frohro/Intro-to-CAD-2026/v0.1/README.md

# Board v0.1

## Hardware

Open [`Hardware/Intro-to-CAD-2026.kicad_pro`](Hardware/Intro-to-CAD-2026.kicad_pro).

## Software

| Path | Role |
|---|---|
| `Software/SDR/MicroPythonSDR/` | Pico MicroPython + Quisk helpers |
| `Software/SDR/Soapy-For-2026-Board/` | Soapy module (from master) |
| `Software/SDR/firmware/96_kHz_2026/` | C UAC1 firmware (restore if missing) |

See `Software/SDR/firmware/README.md` if the firmware folder is empty.
