frohro/Intro-to-CAD-2026/v0.1/Software/SDR/README.md

# v0.1 Software / SDR

- **MicroPythonSDR/** — board Python, Quisk configs/widgets
- **Soapy-For-2026-Board/** — SoapySDR support module
- **firmware/** — native Pico UAC1 projects (see firmware/README.md)
