frohro/Intro-to-CAD-2026/v0.1/Software/SDR/firmware/README.md

# v0.1 SDR firmware

| Folder | Description |
|---|---|
| `96_kHz_2026/` | PCM1808 96 kHz UAC1 firmware for the v0.1 board |

Source: `cptr-480-2026-instructor/Research/96_kHz_2026` (see `README_96kHz_v0.1.md` inside).
