frohro/Intro-to-CAD-2026/v0.2/Hardware/C18594.step

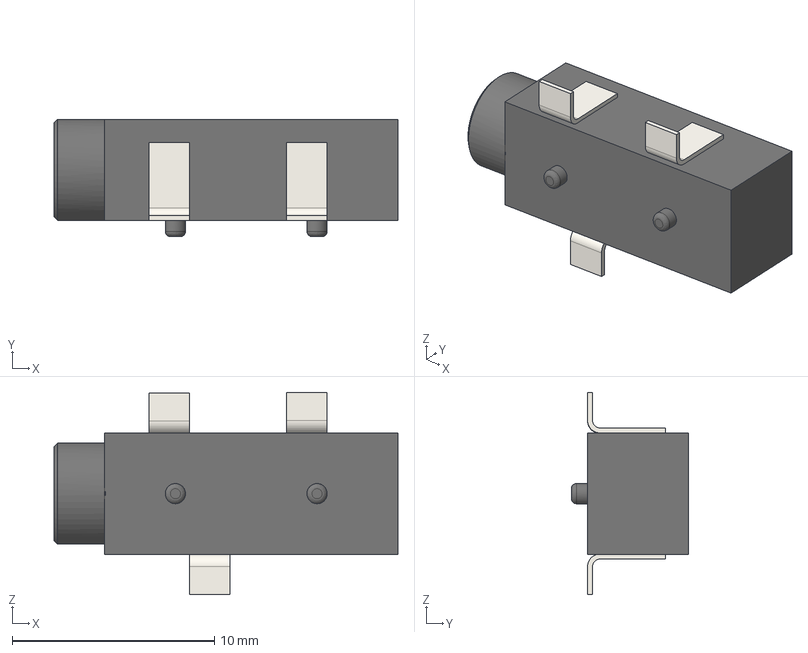
[picture p18: CAD file, 2026-07-31]
v0.2/Hardware/C18594.step
17.0 x 5.80 x 9.98 mm
sj-3524-smt-tr-pi v1 x 5
sj-3524-smt-tr-pi v002 x 5
sj-3524-smt-tr-pi v003 x 2
sj-3524-smt-tr-pi v004 x 2
