frohro/Intro-to-CAD-2026/v0.2/Hardware/Frohne/Docs/DAC_Amp_VBE_Mult.asc

C1: cap; 10µ
C2: cap; 100µ
Q1: npn; FMMT491
Q2: pnp; FMMT591
Q3: npn; FMMT491
R1: res; 1k
R2: res; 10k
R3: res; 2
R4: res; 2
R5: res; 5.1k
R6: res; 5.1k
R7: res; 2.2k
R8: res; 2.2k
R9: res; 32
R10: res; 1k
R11: res; 1k
U1: opamp2; OPA161x
V1: voltage; 5
V2: voltage; SINE(1.6 0.05 10000); Rser=100
Named nets: 0, VCC, VH, Vo, Vi
.tran 0 0.11 0.109
.lib OPA161x.LIB
.include FMMT491.spice.txt
.include FMMT591A.spice.txt
