frohro/Intro-to-CAD-2026/v0.2/Hardware/Frohne/Docs/Noise Amplifier_Balanced_2026._OPA161x.asc

C1: cap; 0.1µ
C3: cap; 0.1µ
C4: cap; 100p
C6: cap; {C_Sample}
C8: cap; 1µF
C13: cap; {C_Sample}
R1: res; 3
R2: res; 3
R3: res; 600k
R4: res; 10k
R5: res; 1k
R6: res; 47
R7: res; 10
R9: res; 1k
R10: res; 10
U1: opamp2; OPA161x
U2: opamp2; OPA161x
V1: voltage; 0; Rser=50
V4: voltage; 4.5
V5: voltage; 2.25
Named nets: +4.5, 0, VGND, V_Q, V_in
;.tran 0 01m 0.5m 10n
;.ac dec 10 10 1000Meg;
.noise V(V_Q) V1 dec 10 1 1MEG
;.op
Power Connections
Simulation Control
;step dec param Audio_freq 1000 10000000 1
.param Audio_freq=10000
This tests the input bias.  It is better without the 15 Ohm risistor on the non-inverting input.
.ic V(N003)=2.25 V(V_Q)=0
.lib OPA161x.LIB
Use Gear in the Simulation->Settings->Spice.
.param C_Sample=10nF
