frohro/Intro-to-CAD-2026/v0.2/Hardware/Frohne/Docs/TayloeDetectorAmplifier_2026.asc

C1: cap; 0.1µ
C2: cap; 150p
C3: cap; 0.1µ
C4: cap; 150p
C7: cap; {C_Sample}
C13: cap; {C_Sample}
I1: current; 250f
I2: current; 250f
I3: current; 250f
I4: current; 250f
L1: ind2; 2m
L2: ind2; 2m
L3: ind2; 2m
R1: res; 10k
R2: res; 15
R4: res; 10k
R5: res; 1k
R6: res; 15
R9: res; 1k
S1: sw; MYSW
S2: sw; MYSW
S3: sw; MYSW
S4: sw; MYSW
S5: sw; MYSW
S6: sw; MYSW
S7: sw; MYSW
S8: sw; MYSW
U1: UniversalOpAmp
U2: UniversalOpAmp
U3: UniversalOpAmp2
U4: UniversalOpAmp2
V1: voltage; PULSE(0 1 0 0 0 {SW_time} {4*SW_time})
V2: voltage; PULSE(0 1 {SW_time} 0 0 {SW_time} {4*SW_time})
V3: voltage; SINE(0 10u {RF_Freq}); AC 1; Rser=50
V4: voltage; 4.5
V5: voltage; 2.25
V6: voltage; PULSE(0 1 {2*SW_time} 0 0{SW_time} {4*SW_time})
V7: voltage; PULSE(0 1 {3*SW_time} 0 0 {SW_time} {4*SW_time})
Named nets: 0, +4.5, VGND, V_0_deg, V_90_deg, V_180_deg, V_270_deg, 00, 11, 01, 10, V_I, V_Q
.model MYSW SW(Vt=0.5 Vh=-0.1 Ron=1 Roff=10Meg)
.tran 0 1m 0.1m
;.ac dec 10 10 1000Meg;
;.noise V(V_Q) V3 dec 10 10 100meg
;.op
.param RF_freq=1Meg LO_freq={RF_freq - Audio_freq} LO_period={1/LO_freq} SW_time={LO_period/4}
.param C_Sample=80pF
Signals for voltage-controlled switches 
used to simulate our multiplexer.
Power Connections
RF signal in
Multiplexer
Simulation Control
;step dec param Audio_freq 1000 10000000 1
.param Audio_freq=10000
The filtering is not just due to the sampling capacitors.  It is also due to the op-amps.
This simulation has the roll off at almost 40 dB/decade without C2.  
You can also see this effect in the peaking at 100 kHz.  C2 removes the peaking,
and makes it drop faster in the first couple of decades, but then the unity gain
zero of the non-inverting amplifier takes over, so it only drops at 40 db/decade
thereafter.
Ideal op amps used as simulation time is long with the ones I am using.
K L1 L2 L3 .9975
This tests the input bias.  It is better without the 15 Ohm risistor on the non-inverting input.
.ic V(VGND)=2.25 V(V_I)=2.25 V(V_Q)=2.25
