frohro/Intro-to-CAD-2026/v0.2/Software/SDR/firmware/192_kHz_CJC_5340_2026_v0.2/quisk_conf_192k.py

# Quisk configuration for the Intro-to-CAD-2026 Pico SDR board
# Research version: fixed 192 kHz (S16_LE over USB)
#
# Firmware captures 24-bit samples and streams dithered 16-bit audio at 192 kHz.
# Keep Quisk and firmware sample rates matched.

from __future__ import print_function
from __future__ import absolute_import
from __future__ import division

import os

name_of_sound_capt = "alsa:WWU SDR USB Audio (hw:3,0)"  # PortAudio ALSA device name as shown in Quisk Config -> Radio -> Sound
                                                        # The hw:X,0 card number varies by machine; select the correct
                                                        # device in Quisk's Config screen and it will update this value.
name_of_sound_play = "pulse"    # Playback through PipeWire/PulseAudio

sample_rate = 192000

# At 192 kHz Quisk's DSP load is significantly higher. A larger output
# buffer helps absorb transient CPU spikes and avoid underruns.
lin_latency_millisecs = 700

openradio_lower = 3_800_000
openradio_upper = 30_000_000

widgets_file_name = os.path.join(os.path.dirname(__file__), "quisk_widgets_2026.py")

import math
import fractions
import serial
import time
from quisk_hardware_model import Hardware as BaseHardware


class Hardware(BaseHardware):
    def open(self):
        """Open the serial connection to the Pico and configure it."""
        baud = 115200
        for port in ("/dev/ttyACM0", "/dev/ttyACM1"):
            try:
                self.or_serial = serial.Serial(port, baud, timeout=3)
                print("Opened", port)
                break
            except serial.serialutil.SerialException:
                continue
        else:
            raise serial.serialutil.SerialException(
                "Pico not found on /dev/ttyACM0 or /dev/ttyACM1")

        self.or_serial.write(b'\x03')
        time.sleep(0.1)
        self.or_serial.write(b'\x04')
        self.or_serial.reset_input_buffer()

        self.or_serial.timeout = 0.2
        deadline = time.time() + 6.0
        while time.time() < deadline:
            line = self.or_serial.readline()
            if b'SDR ready' in line:
                break
        self.or_serial.timeout = 3

        version = str(self._get_parameter("VER"))
        print("Pico firmware:", version)

        xtal_raw = self._get_parameter("XTAL")
        try:
            self._crystal_freq = float(xtal_raw)
            if self._crystal_freq <= 0:
                raise ValueError("invalid")
        except (ValueError, TypeError):
            self._crystal_freq = 24_576_000.0
        print("Crystal freq: %.3f Hz" % self._crystal_freq)

        self._set_parameter("RATE", str(sample_rate))

        self._golden_status = "PLL: ready"
        self._last_lo = None
        self._comparison_use_worst = False
        self._comparison_pair = None
        self._comparison_candidates = []
        self._last_tune = None
        self._active_candidate = None

        return version + ". Capture from %s at %d Hz." % (
            self.conf.name_of_sound_capt, sample_rate)

    def close(self):
        self.or_serial.close()

    def _candidate_from_values(self, tune, lo_hz, n_value, a_value, b_value, c_value):
        tune_hz = int(round(tune))
        lo_hz = int(round(lo_hz))
        floor_term = math.floor(128 * b_value / c_value)
        p1 = int(128 * a_value + floor_term - 512)
        p2 = int(128 * b_value - c_value * floor_term)
        p3 = int(c_value)
        return {
            "tune": tune_hz,
            "lo": lo_hz,
            "signed_offset": lo_hz - tune_hz,
            "n": int(n_value),
            "a": int(a_value),
            "b": int(b_value),
            "c": int(c_value),
            "p1": p1,
            "p2": p2,
            "p3": p3,
            "ptype": "G" if int(b_value) == 0 else "F",
        }

    def _candidate_for_lo(self, tune, lo_hz):
        lo_hz = int(round(lo_hz))
        crystal = self._crystal_freq

        best_n = None
        exact_m = None
        n_min = max(6, int(math.ceil(600_000_000.0 / lo_hz)))
        n_max = min(126, int(900_000_000.0 / lo_hz))

        for n_cand in range(n_min if n_min % 2 == 0 else n_min + 1, n_max + 1, 2):
            m_float = lo_hz * n_cand / crystal
            if not (14 < m_float < 91):
                continue
            m_int = round(m_float)
            if abs(m_float - m_int) < 1e-6:
                best_n = n_cand
                exact_m = m_int
                break

        if best_n is not None:
            return self._candidate_from_values(tune, lo_hz, best_n, exact_m, 0, 1)

        n_value = n_min if n_min % 2 == 0 else n_min + 1
        frac = fractions.Fraction(int(lo_hz * n_value), int(crystal)).limit_denominator(1048575)
        a_value = int(frac)
        b_value = frac.numerator - a_value * frac.denominator
        c_value = frac.denominator
        return self._candidate_from_values(tune, lo_hz, n_value, a_value, b_value, c_value)

    def _candidate_rank_key(self, candidate):
        quarter = sample_rate // 4
        return (
            abs(abs(candidate["signed_offset"]) - quarter),
            abs(candidate["signed_offset"]),
            candidate["n"],
        )

    def _comparison_label(self):
        return "WORST" if self._comparison_use_worst else "BEST"

    def _format_candidate(self, label, candidate):
        return (
            "%s LO=%dHz off=%+dHz N=%d M=%d+%d/%d P1=%d P2=%d P3=%d" % (
                label,
                candidate["lo"],
                candidate["signed_offset"],
                candidate["n"],
                candidate["a"],
                candidate["b"],
                candidate["c"],
                candidate["p1"],
                candidate["p2"],
                candidate["p3"],
            )
        )

    def _widget_summary(self):
        if not self._comparison_pair:
            return "Best/Worst integers not ready"

        best = self._comparison_pair["best"]
        worst = self._comparison_pair["worst"]
        mode = self._comparison_label()
        if self._comparison_pair["integer_count"] <= 0:
            return "%s fallback LO=%dHz off=%+dHz" % (
                mode,
                best["lo"],
                best["signed_offset"],
            )
        if self._comparison_pair["integer_count"] == 1:
            return "%s only integer LO N=%d off=%+dHz" % (
                mode,
                best["n"],
                best["signed_offset"],
            )
        return (
            "%s best N=%d off=%+dHz | worst N=%d off=%+dHz" % (
                mode,
                best["n"],
                best["signed_offset"],
                worst["n"],
                worst["signed_offset"],
            )
        )

    def _refresh_widget_status(self):
        bottom = getattr(self.app, "bottom_widgets", None)
        if bottom and hasattr(bottom, "UpdateStatus"):
            bottom.UpdateStatus()

    def _log_comparison_pair(self):
        if not self._comparison_pair:
            return
        print(self._format_candidate("BEST", self._comparison_pair["best"]))
        if self._comparison_pair["integer_count"] > 1:
            print(self._format_candidate("WORST", self._comparison_pair["worst"]))
        elif self._comparison_pair["integer_count"] == 1:
            print("WORST same as BEST: only one valid integer LO in the overlapping IF windows")
        else:
            print("No valid integer LO pair; using fractional fallback")

    def _select_comparison_pair(self, tune):
        candidates = self._find_integer_candidates(tune)
        self._comparison_candidates = candidates
        if candidates:
            ordered = sorted(candidates, key=self._candidate_rank_key)
            best = ordered[0]
            worst = ordered[-1]
            pair = {
                "best": best,
                "worst": worst,
                "integer_count": len(ordered),
            }
        else:
            fallback = self._candidate_for_lo(tune, int(round(tune - sample_rate // 4)))
            pair = {
                "best": fallback,
                "worst": fallback,
                "integer_count": 0,
            }
        self._comparison_pair = pair
        return pair

    def active_comparison_candidate(self):
        if not self._comparison_pair:
            return None
        key = "worst" if self._comparison_use_worst else "best"
        return self._comparison_pair[key]

    def set_comparison_mode(self, use_worst):
        self._comparison_use_worst = bool(use_worst)
        candidate = self.active_comparison_candidate()
        if candidate is not None:
            self._program_candidate(candidate, self._comparison_label())
        self._refresh_widget_status()

    def _find_integer_candidates(self, tune):
        half_bw = sample_rate // 2
        crystal = self._crystal_freq
        n_min = max(4, int(math.ceil(600_000_000.0 / tune)))
        n_max = min(127, int(900_000_000.0 / tune))
        results = []
        for n_cand in range(n_min if n_min % 2 == 0 else n_min + 1, n_max + 1, 2):
            m_float = tune * n_cand / crystal
            if not (14 < m_float < 91):
                continue
            m_int = round(m_float)
            lo = crystal * m_int / n_cand
            signed = lo - tune
            if abs(signed) < half_bw:
                candidate = self._candidate_from_values(tune, lo, n_cand, m_int, 0, 1)
                results.append(candidate)
        return results

    def _find_golden_los(self, tune):
        ordered = sorted(self._find_integer_candidates(tune), key=self._candidate_rank_key)
        return [(candidate["lo"], candidate["signed_offset"]) for candidate in ordered]

    def _program_lo(self, lo_hz):
        candidate = self._candidate_for_lo(lo_hz, lo_hz)
        return self._program_candidate(candidate, None)

    def _program_candidate(self, candidate, label):
        tune = candidate["lo"]
        self._send(
            f"FREQ,{tune},{candidate['n']},{candidate['a']},{candidate['b']},{candidate['c']},{candidate['p1']},{candidate['p2']},{candidate['p3']}"
        )
        self._readline()
        ok_line = self._readline().decode(errors='replace').strip()
        self._last_lo = candidate["lo"]
        self._active_candidate = dict(candidate)
        parts = ok_line.split(",")
        signed_offset = 0
        if len(parts) >= 3 and parts[0] == "OK":
            ptype = parts[1]
            try:
                signed_offset = int(parts[2])
            except ValueError:
                signed_offset = 0
            if ptype == "G":
                prefix = label or "PLL"
                self._golden_status = "%s  {:+d} Hz  N=%d M=%d+%d/%d".format(signed_offset) % (
                    prefix,
                    candidate["n"],
                    candidate["a"],
                    candidate["b"],
                    candidate["c"],
                )
            elif ptype == "F":
                self._golden_status = "frac  (exact freq)"
            else:
                self._golden_status = "fallback  (VCO out of spec)"
        self._refresh_widget_status()
        return signed_offset

    def ChangeFrequency(self, tune, vfo, source='', band='', event=None):
        tune = max(openradio_lower, min(openradio_upper, tune))
        half_bw = sample_rate // 2
        quarter = sample_rate // 4
        self._last_tune = int(round(tune))

        pair = self._select_comparison_pair(tune)
        golden = [(candidate["lo"], candidate["signed_offset"]) for candidate in self._comparison_candidates]

        is_arrow = (
            self._last_lo is not None and
            abs(vfo - self._last_lo) > 100 and
            abs(vfo - self._last_lo) < half_bw
        )

        if is_arrow:
            direction = 1 if vfo > self._last_lo else -1
            candidates = [
                (abs(lo - self._last_lo), lo, signed)
                for (lo, signed) in golden
                if (lo - self._last_lo) * direction > 0
            ]
            if candidates:
                candidates.sort()
                chosen_lo = candidates[0][1]
            else:
                shift = direction * quarter
                new_lo = self._last_lo + shift
                guard = 2000
                new_lo = max(tune - half_bw + guard, min(tune + half_bw - guard, new_lo))
                chosen_lo = new_lo
            candidate = self._candidate_for_lo(tune, chosen_lo)
            label = "ARROW"
        else:
            candidate = self.active_comparison_candidate()
            if candidate is None:
                candidate = pair["best"]
            chosen_lo = candidate["lo"]
            label = self._comparison_label()
            self._log_comparison_pair()

        chosen_lo = int(max(openradio_lower, min(openradio_upper, chosen_lo)))
        if candidate["lo"] != chosen_lo:
            candidate = self._candidate_for_lo(tune, chosen_lo)
        self._program_candidate(candidate, label)
        return int(tune), int(chosen_lo)

    def HeartBeat(self):
        try:
            self.app.StatusScreen(self._golden_status)
            self._refresh_widget_status()
        except Exception:
            pass

    def _send(self, line):
        self.or_serial.write((line + "\n").encode())

    def _readline(self):
        return self.or_serial.readline()

    def _get_parameter(self, cmd):
        self._send(cmd)
        return self._get_argument()

    def _set_parameter(self, cmd, arg):
        self._send(cmd + "," + arg)
        self._get_argument()
        return True

    def _get_argument(self):
        for _ in range(5):
            data = self._readline()
            if len(data) == 0:
                return -1
            if data.startswith(b'OK'):
                continue
            if data.find(b',') != -1:
                value = data.split(b',')[1].rstrip(b'\r\n')
                self._readline()
                return value.decode(errors='replace')
        return -1
